tomykaira/rotenc_keyboard/keymap/config.h

/*
This is the c configuration file for the keymap

Copyright 2012 Jun Wako <wakojun@gmail.com>
Copyright 2015 Jack Humbert

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
You should have received a copy of the GNU General Public License
along with this program.  If not, see <http://www.gnu.org/licenses/>.
*/

#ifndef CONFIG_USER_H
#define CONFIG_USER_H

#include "../../config.h"

/* Use I2C or Serial, not both */

#define USE_SERIAL
// #define USE_I2C

/* Select hand configuration */

#define MASTER_RIGHT
// #define EE_HANDS

#undef  TAPPING_TERM
#define TAPPING_TERM 300

#undef RETRO_TAPPING
#undef PERMISSIVE_HOLD

#define PREVENT_STUCK_MODIFIERS

#define USB_MAX_POWER_CONSUMPTION 100

#define DISABLE_JTAG

#endif
